jhrg/nixie-2/docs/Anode_on_and_tube_voltage.png

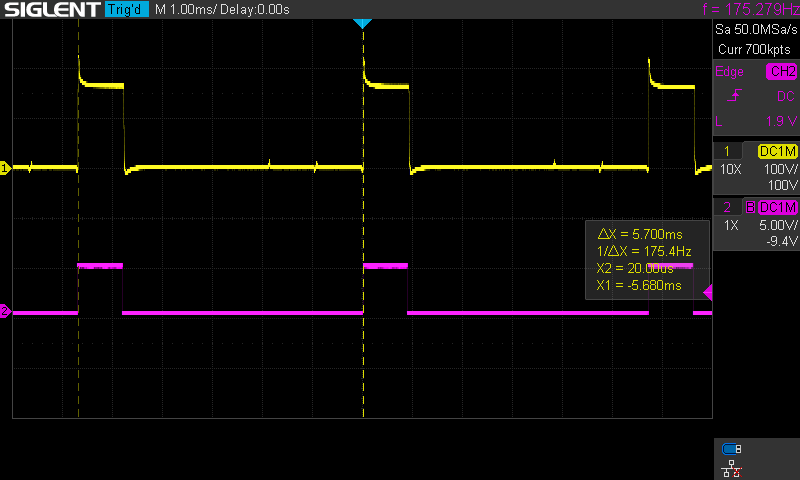
docs/Anode_on_and_tube_voltage.png
