jhrg/nixie-2/docs/Anode_shunt_resistor/Anode_10x_with_220k.png

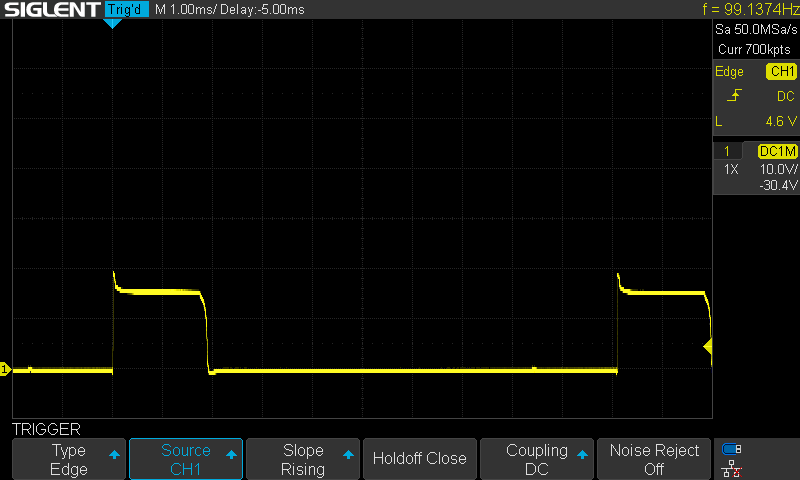
docs/Anode_shunt_resistor/Anode_10x_with_220k.png
