jhrg/nixie-2/docs/Anode_shunt_resistor/Tube_1M_anode_res.png

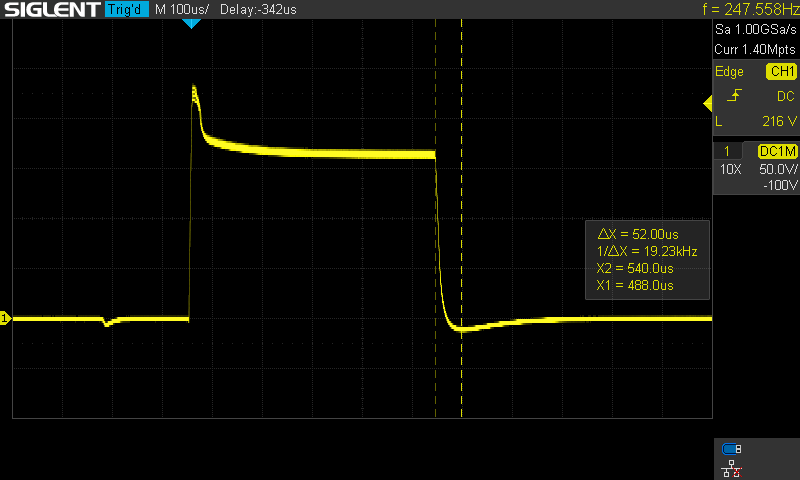
docs/Anode_shunt_resistor/Tube_1M_anode_res.png
