jhrg/nixie-2/docs/Anode_shunt_resistor/Tube_off_delay_24uS_no_anode_res.png

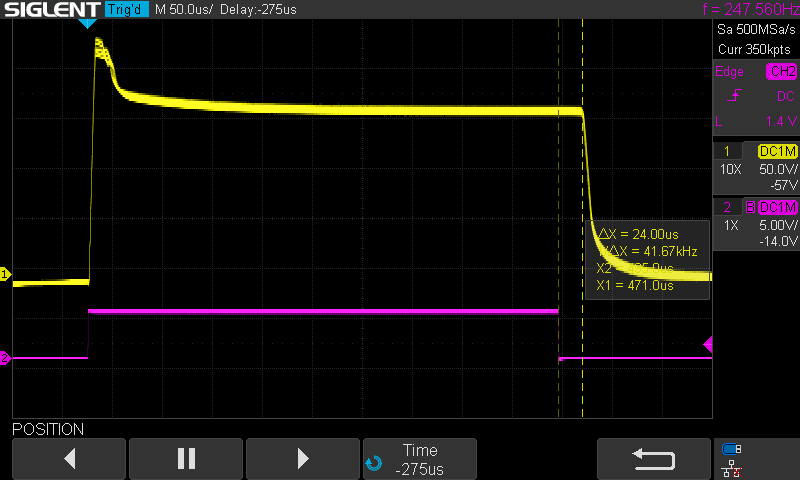
docs/Anode_shunt_resistor/Tube_off_delay_24uS_no_anode_res.png
