jhrg/nixie-2/docs/AVR_HV_PS/Load_34%D.png

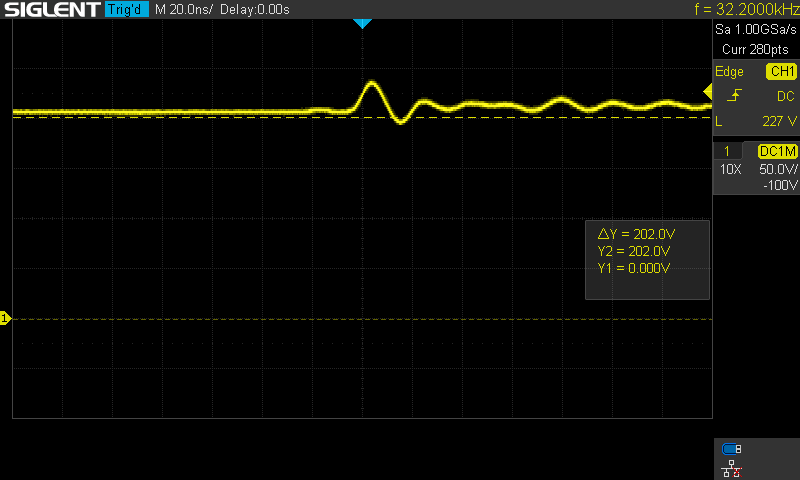
docs/AVR_HV_PS/Load_34%D.png
