jhrg/nixie-2/docs/AVR_HV_PS/Ripple_high.png

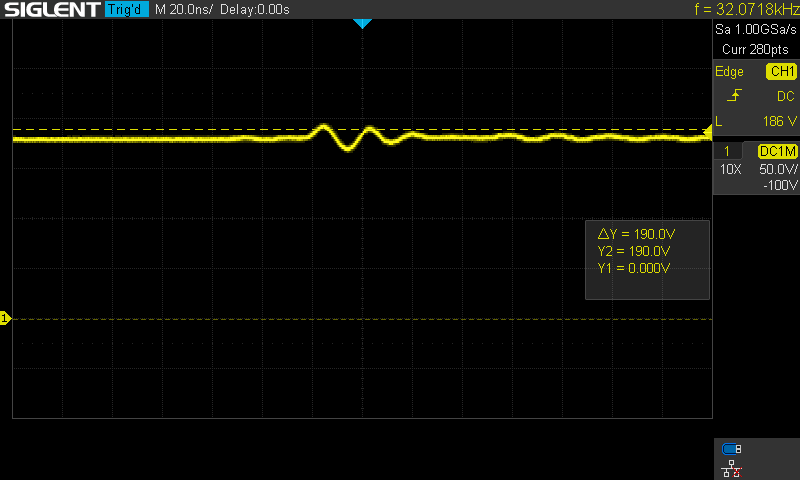
docs/AVR_HV_PS/Ripple_high.png
