jhrg/nixie-2/docs/Digit_blanking_ITR_time.png

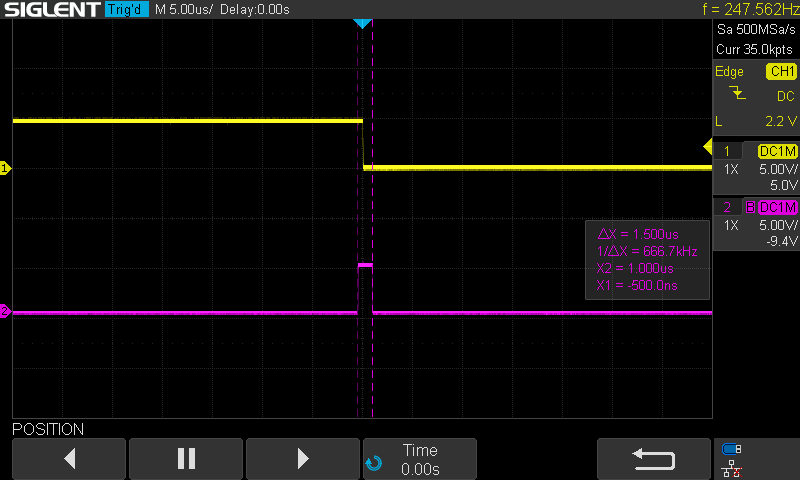
docs/Digit_blanking_ITR_time.png
