jhrg/nixie-2/docs/Digit_on_ITR_time.png

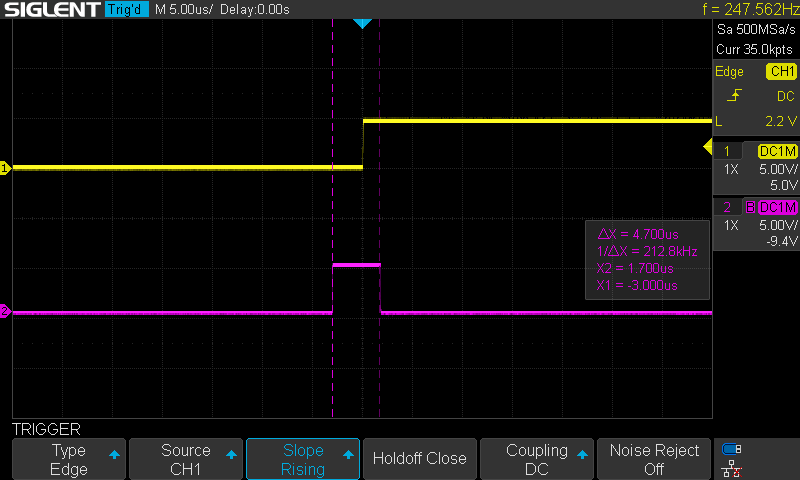
docs/Digit_on_ITR_time.png
