jhrg/nixie-2/docs/Digit_transition_10.18.22.png

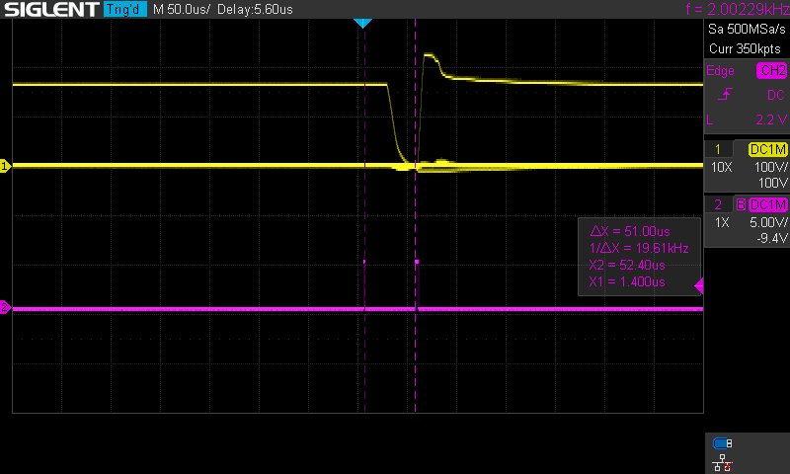
docs/Digit_transition_10.18.22.png
