jhrg/nixie-2/docs/Fixed_Timer2_ISR/Digit_blanking_time_60uS.png

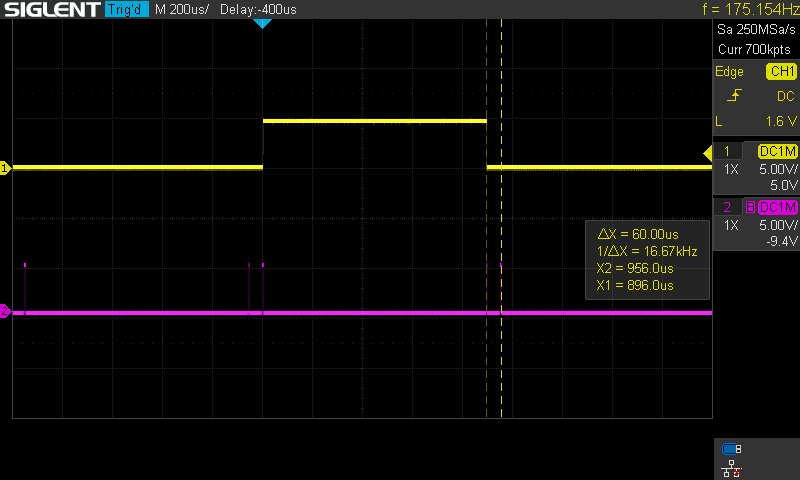
docs/Fixed_Timer2_ISR/Digit_blanking_time_60uS.png
