jhrg/nixie-2/docs/Fixed_Timer2_ISR/Digit_on_time_900uS.png

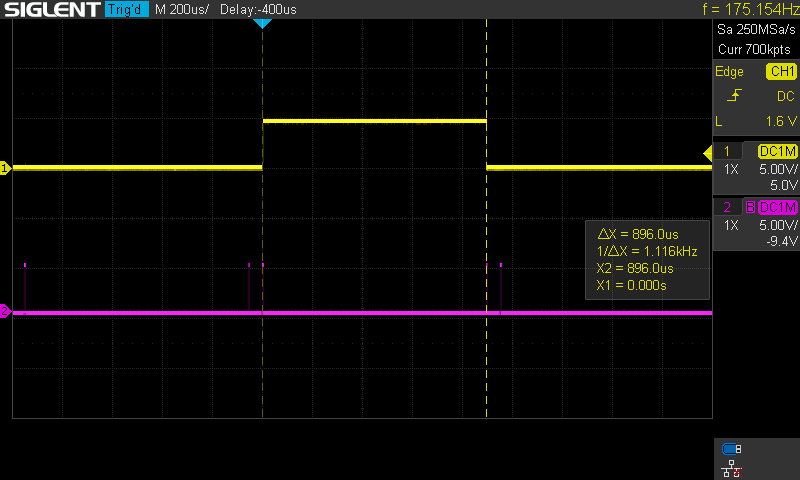
docs/Fixed_Timer2_ISR/Digit_on_time_900uS.png
