jhrg/nixie-2/docs/Fixed_Timer2_ISR/Digit_shutdown_time_30uS.png

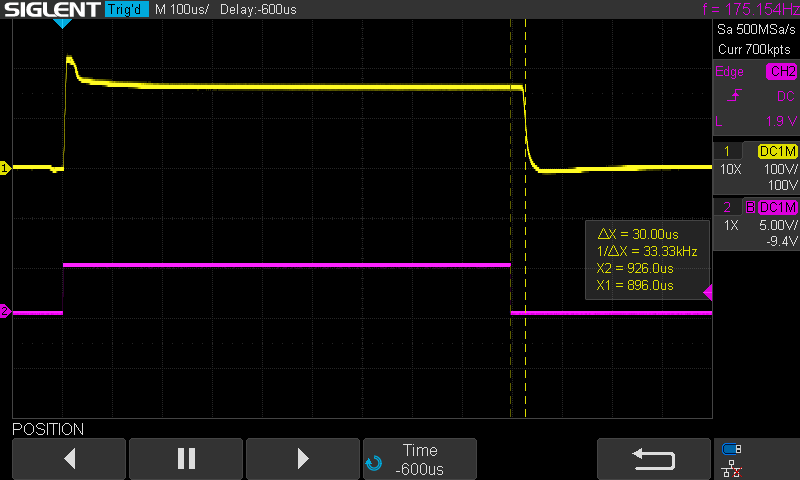
docs/Fixed_Timer2_ISR/Digit_shutdown_time_30uS.png
