jhrg/nixie-2/docs/Fixed_Timer2_ISR/Period_for_6_Digit_cycle_5.7ms.png

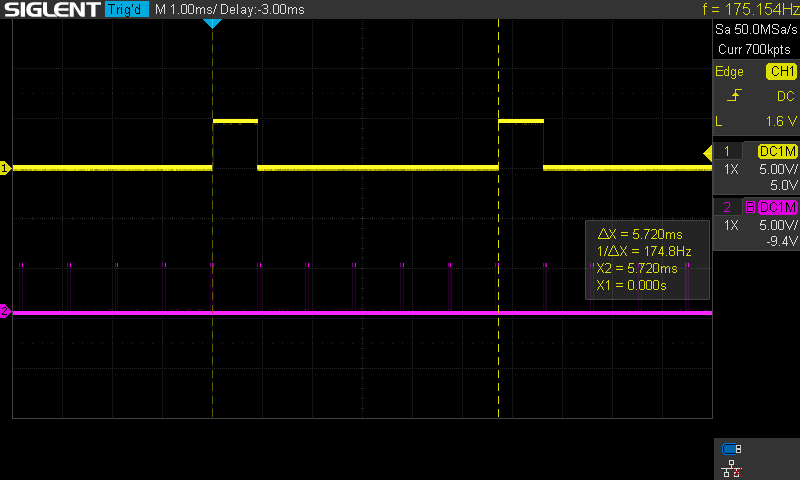
docs/Fixed_Timer2_ISR/Period_for_6_Digit_cycle_5.7ms.png
