jhrg/nixie-2/docs/Ionization_time/1Hz_4.7k_200v_tube_voltage.png

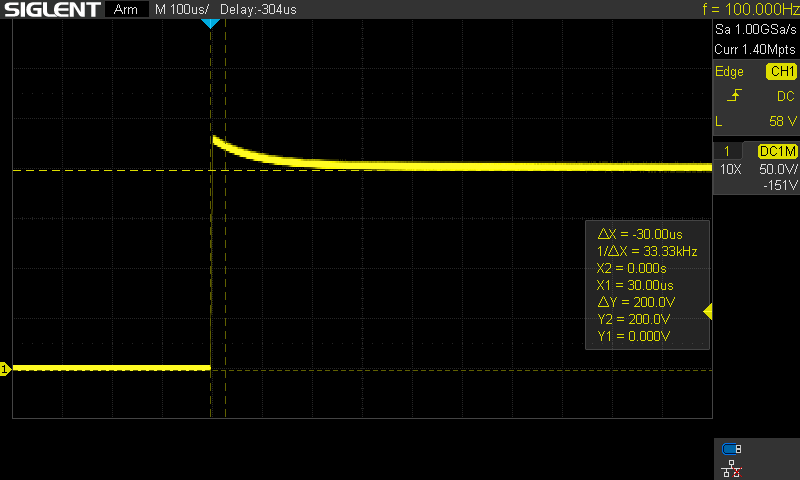
docs/Ionization_time/1Hz_4.7k_200v_tube_voltage.png
