jhrg/nixie-2/docs/Ionization_time/Time_to_ionize_at_Vs_180v.png

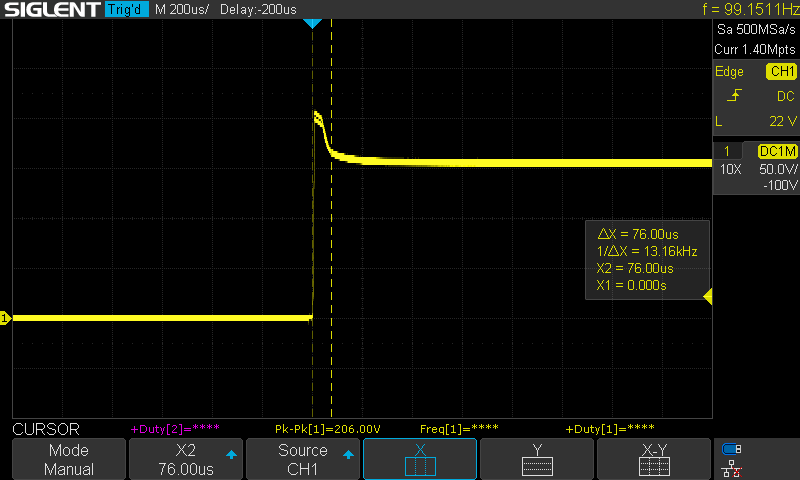
docs/Ionization_time/Time_to_ionize_at_Vs_180v.png
