jhrg/nixie-2/docs/New_digit_blanksing_ITR_time.png

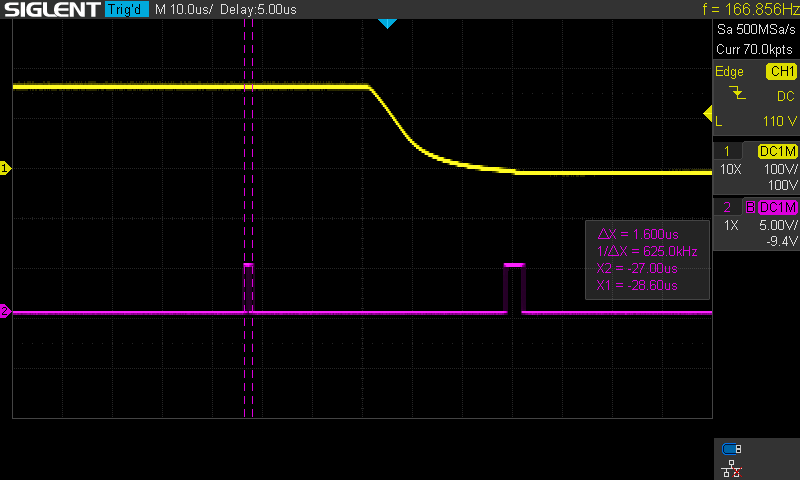
docs/New_digit_blanksing_ITR_time.png
