jhrg/nixie-2/docs/New_digit_on_ITR_time.png

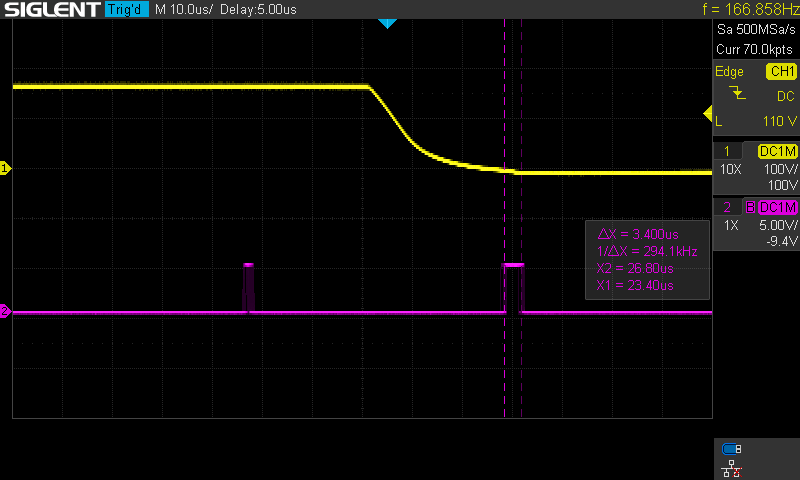
docs/New_digit_on_ITR_time.png
