jhrg/nixie-2/docs/New_timing_code_anode_off_time.png

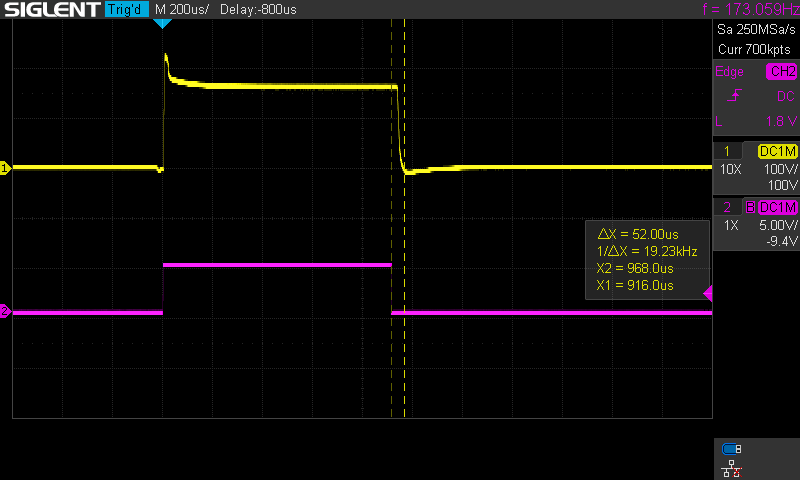
docs/New_timing_code_anode_off_time.png
