jhrg/nixie-2/docs/Nixie_FLIR_Pictures/Front_view_1.JPG

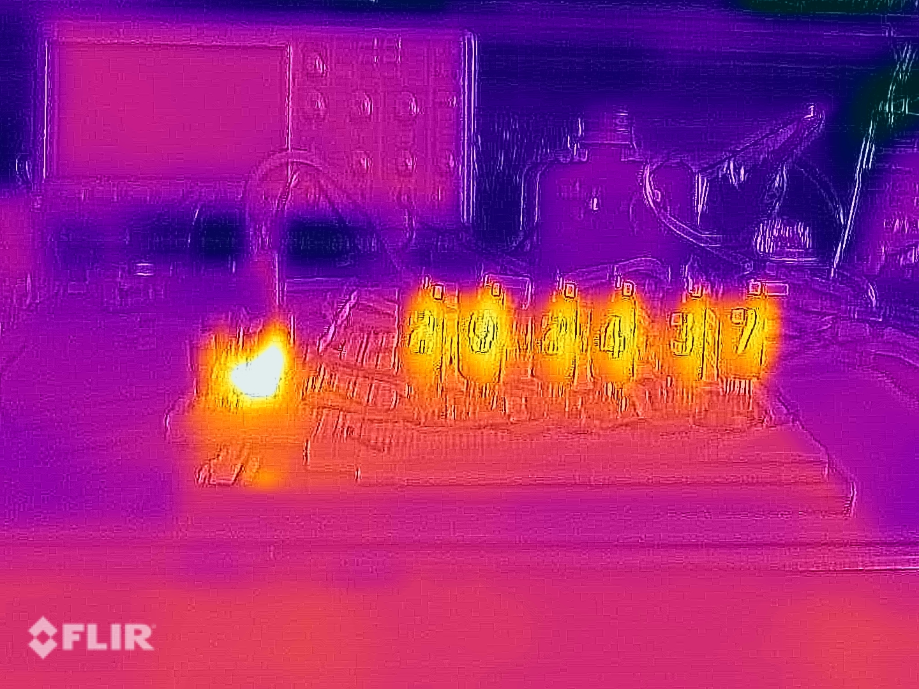
docs/Nixie_FLIR_Pictures/Front_view_1.JPG
