jhrg/nixie-2/docs/Nixie_FLIR_Pictures/HV_PS_1.JPG

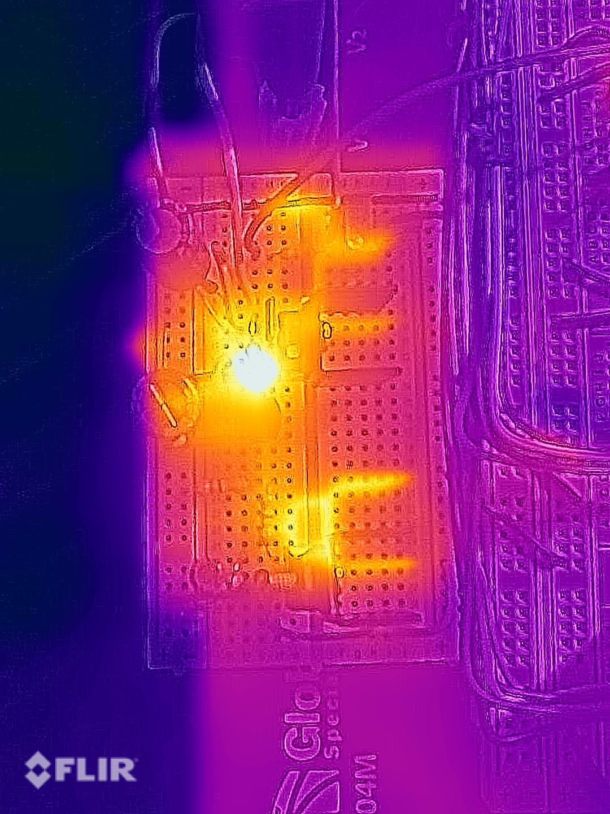
docs/Nixie_FLIR_Pictures/HV_PS_1.JPG
