jhrg/nixie-2/docs/Nixie_FLIR_Pictures/IN-14_front.JPG

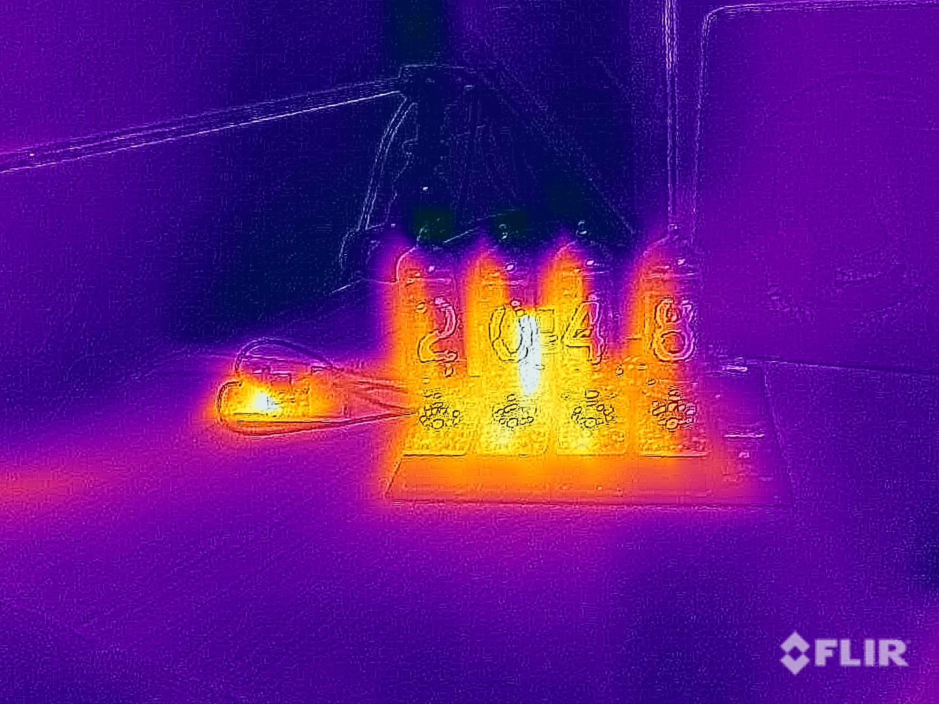
docs/Nixie_FLIR_Pictures/IN-14_front.JPG
