jhrg/nixie-2/docs/Nixie_FLIR_Pictures/Top_view_2.JPG

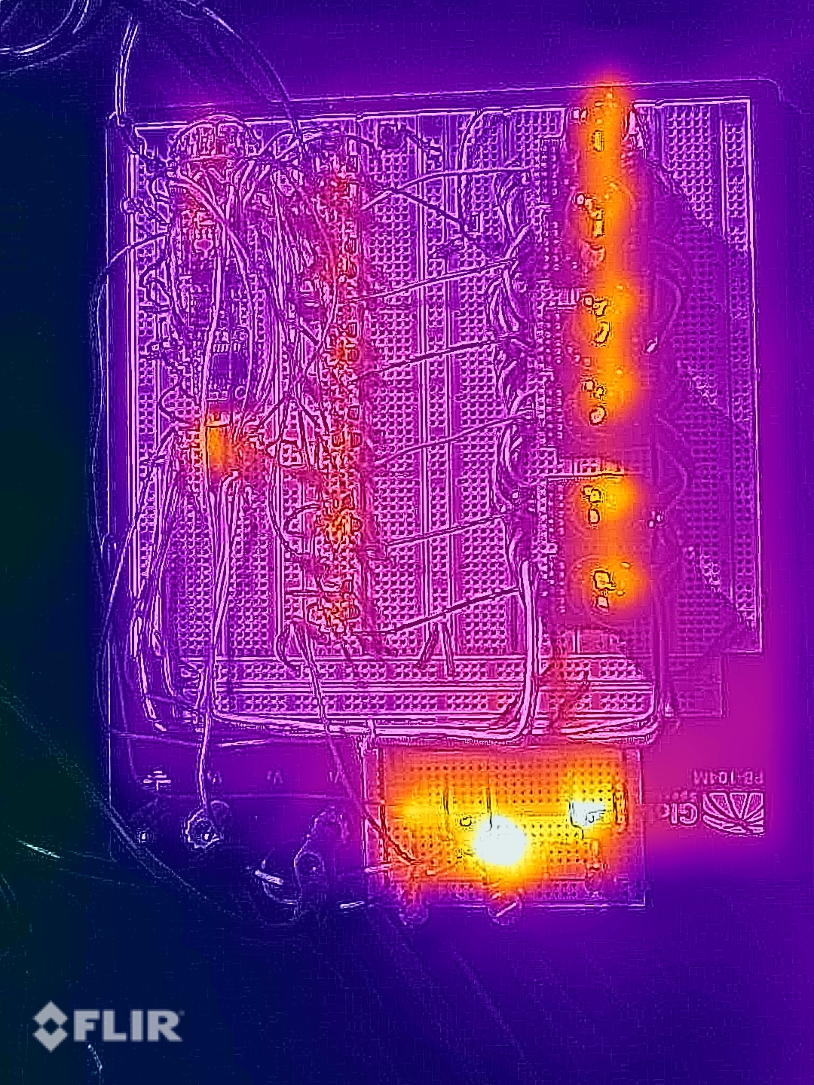
docs/Nixie_FLIR_Pictures/Top_view_2.JPG
