jhrg/nixie-2/docs/Nixie_FLIR_Pictures/Top_view_close_1.JPG

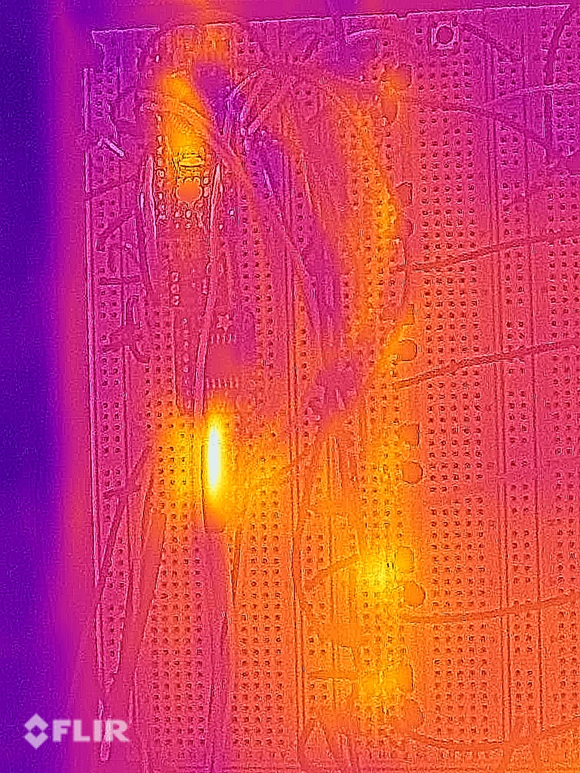
docs/Nixie_FLIR_Pictures/Top_view_close_1.JPG
