jhrg/nixie-2/docs/V_anode.png

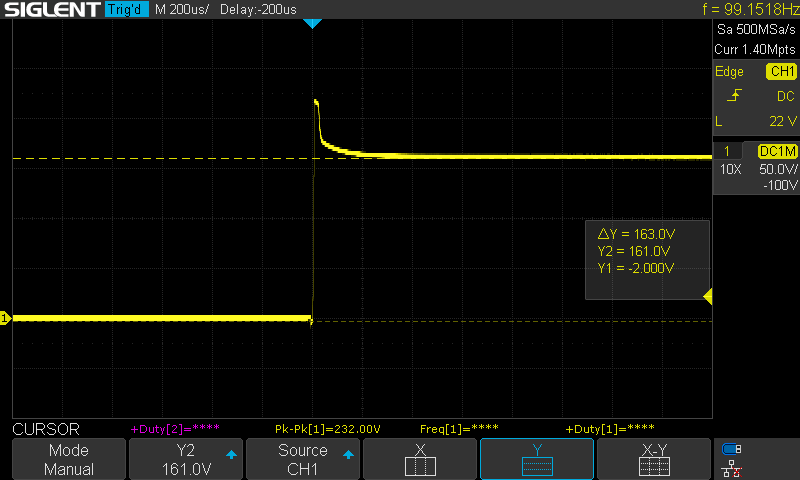
docs/V_anode.png
