jhrg/nixie-2/docs/Voltage_R_anode_Vs_200_Vm_166.png

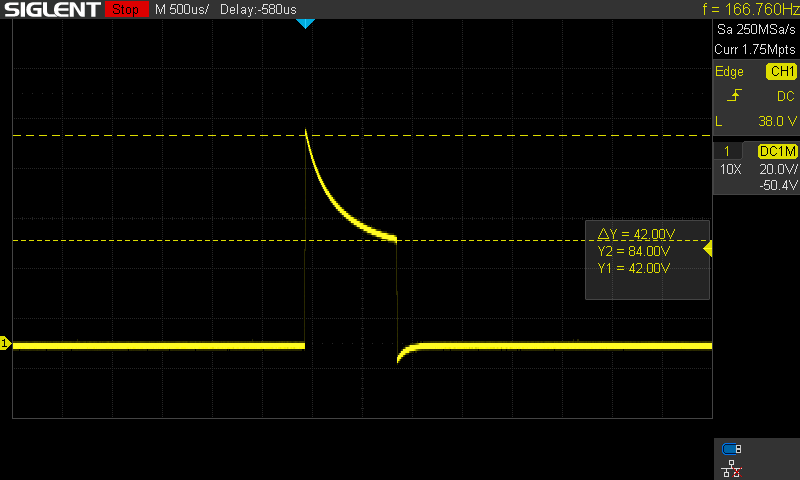
docs/Voltage_R_anode_Vs_200_Vm_166.png
